jguillaumes/MeteoArduino/sensors/ReadLight.h

/*
 * ReadLight.h
 *
 *  Created on: Jan 29, 2018
 *      Author: jguillaumes
 */

#ifndef READLIGHT_H_
#define READLIGHT_H_

// Arduino NANO: A6
// Standalone:   A3
#define LIGHT_PIN	A3


int lightInitialize(void);
float lightRead(void);

#endif /* READLIGHT_H_ */
